felixJR123/Snake-Dongle-Case/Pictures/Waveshare Screen Version/20260205_205230.jpg

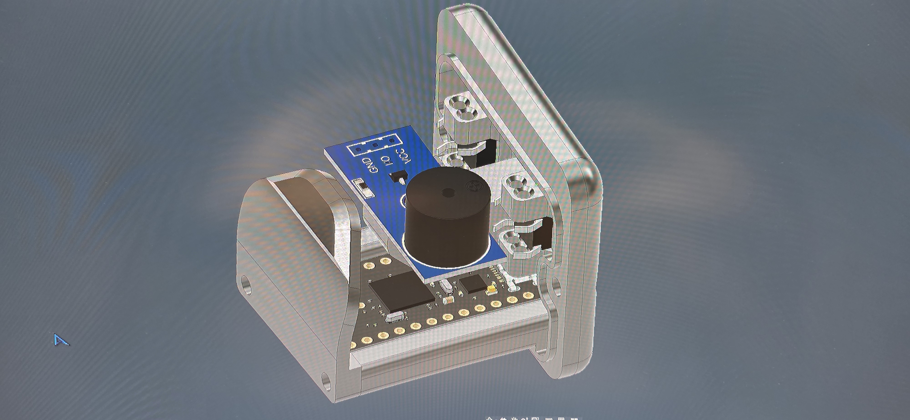
Pictures/Waveshare Screen Version/20260205_205230.jpg
