felixJR123/Snake-Dongle-Case/Pictures/Waveshare Screen Version/20260205_205346.jpg

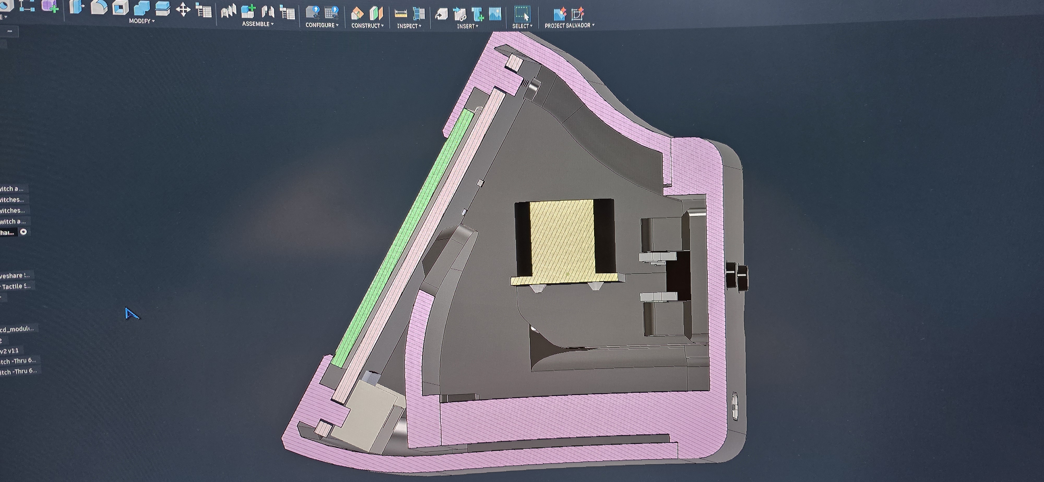
Pictures/Waveshare Screen Version/20260205_205346.jpg
